shaheenbharwani/sim2real-3d-printed-quadruped/hardware/urdf/meshes/mesh163.obj

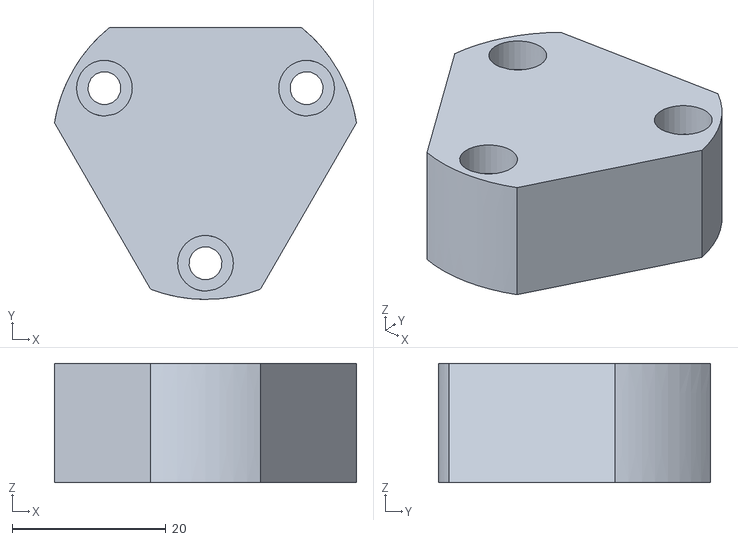
[picture p12: CAD file, 2025-07-08]
hardware/urdf/meshes/mesh163.obj
39.3 x 35.3 x 15.5
