shaheenbharwani/sim2real-3d-printed-quadruped/hardware/urdf/meshes/mesh92.obj

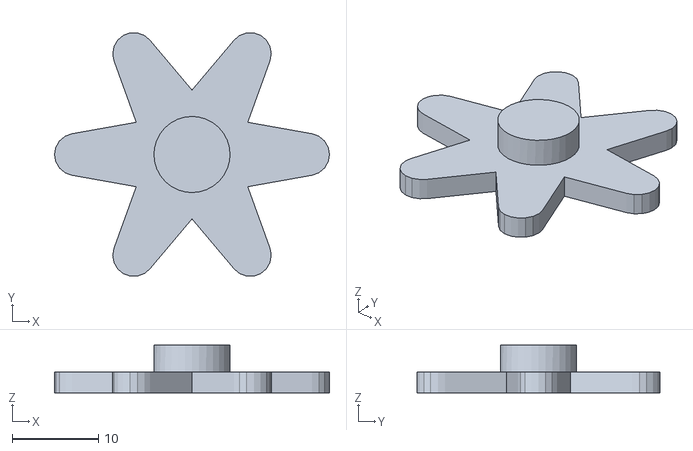
[picture p13: CAD file, 2025-07-08]
hardware/urdf/meshes/mesh92.obj
31.8 x 28.1 x 5.50
