shaheenbharwani/sim2real-3d-printed-quadruped/hardware/urdf/meshes/mesh118.obj

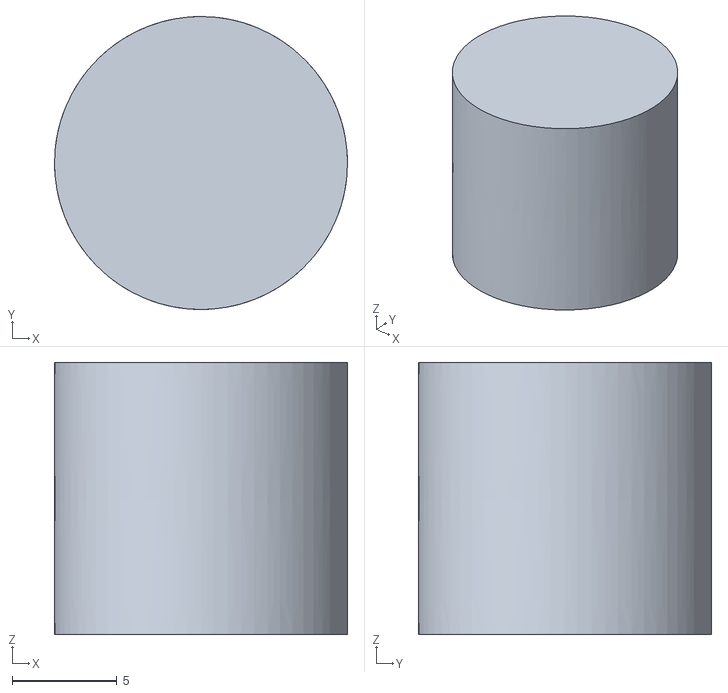
[picture p14: CAD file, 2025-07-08]
hardware/urdf/meshes/mesh118.obj
14.0 x 14.0 x 13.0
