shaheenbharwani/sim2real-3d-printed-quadruped/hardware/urdf/meshes/mesh71.obj

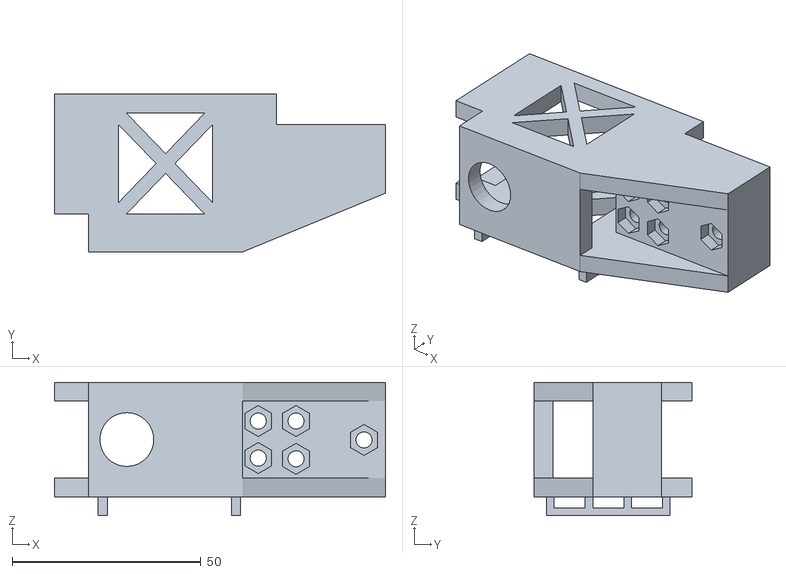
[picture p15: CAD file, 2025-07-08]
hardware/urdf/meshes/mesh71.obj
87.6 x 41.8 x 35.3
