shaheenbharwani/sim2real-3d-printed-quadruped/hardware/urdf/meshes/mesh1.obj

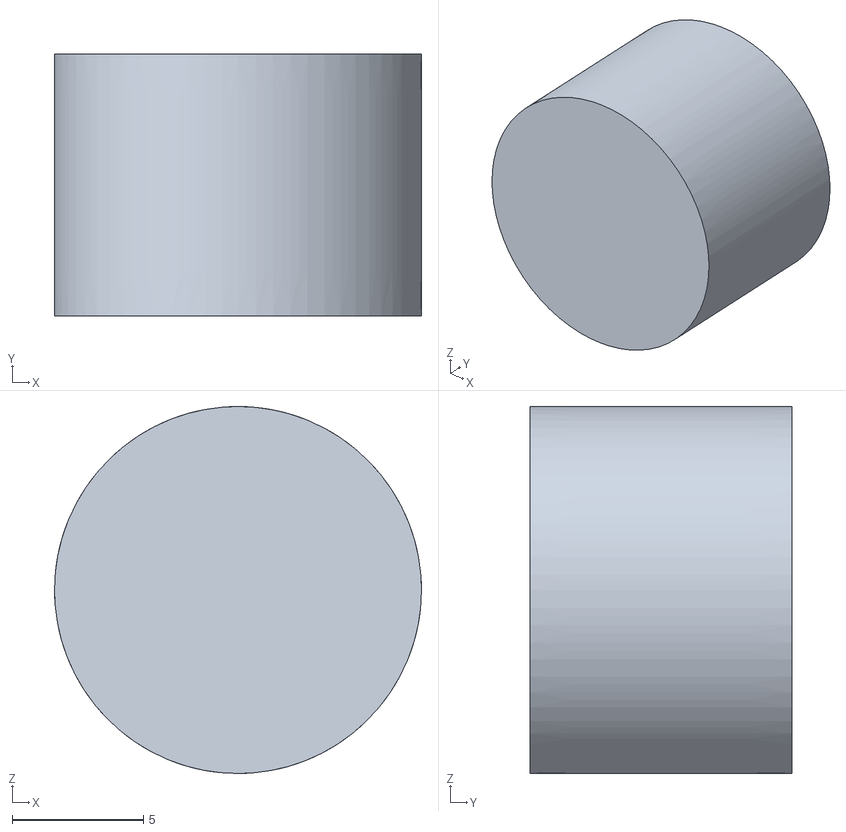
[picture p16: CAD file, 2025-07-08]
hardware/urdf/meshes/mesh1.obj
14.0 x 10.0 x 14.0
