shaheenbharwani/sim2real-3d-printed-quadruped/hardware/urdf/meshes/mesh164.obj

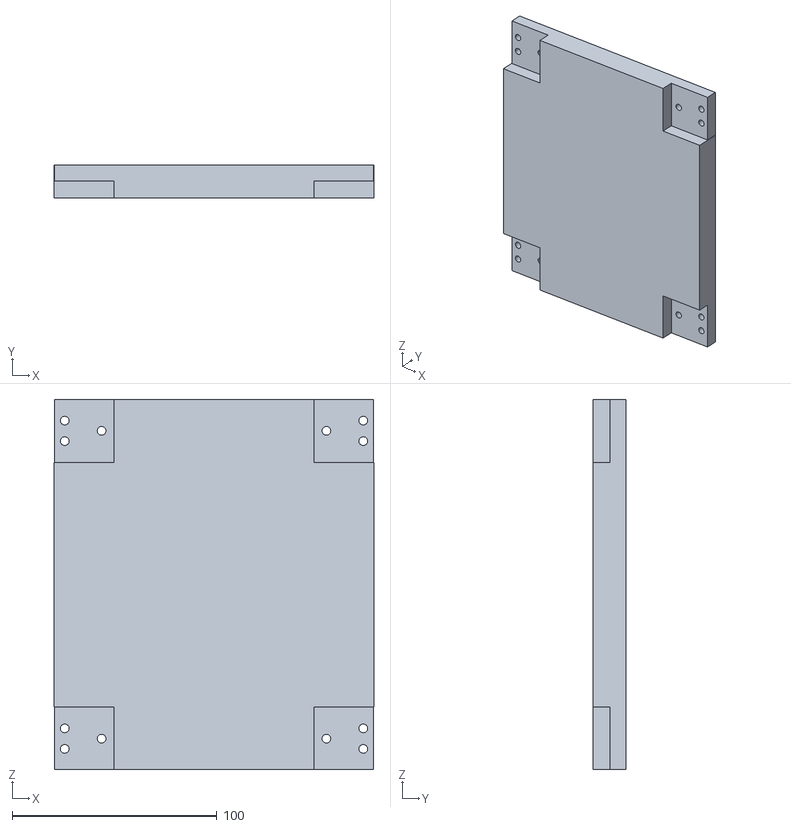
[picture p17: CAD file, 2025-07-08]
hardware/urdf/meshes/mesh164.obj
156.0 x 16.3 x 180.5
