shaheenbharwani/sim2real-3d-printed-quadruped/hardware/urdf/meshes/mesh77.obj

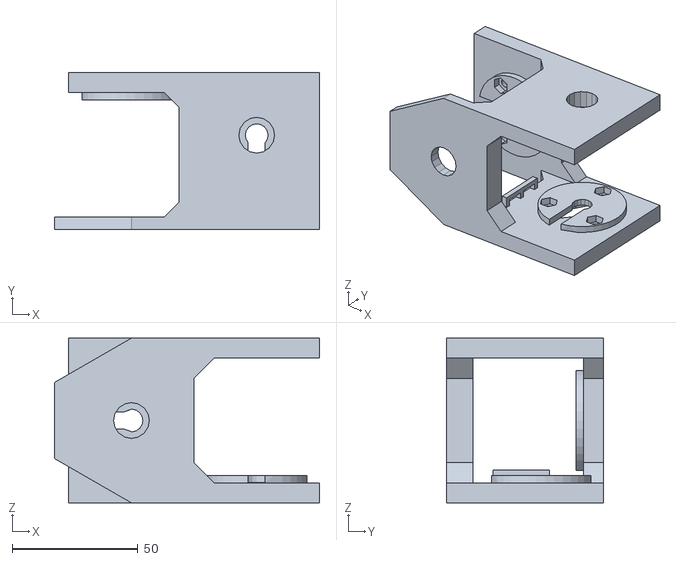
[picture p18: CAD file, 2025-07-08]
hardware/urdf/meshes/mesh77.obj
105.5 x 62.6 x 65.6
