shaheenbharwani/sim2real-3d-printed-quadruped/hardware/urdf/meshes/mesh160.obj

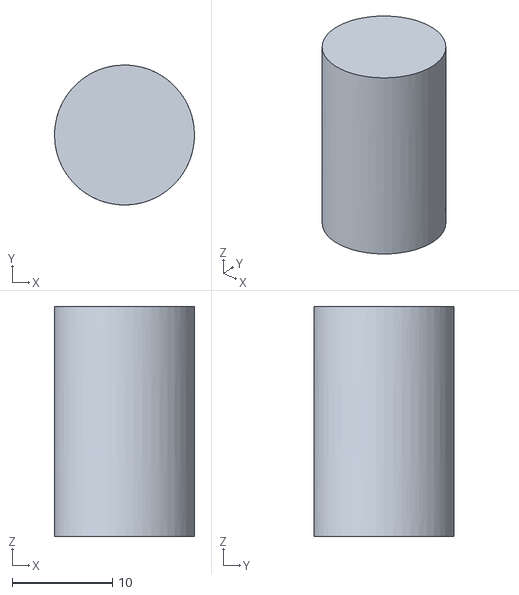
[picture p19: CAD file, 2025-07-08]
hardware/urdf/meshes/mesh160.obj
14.0 x 14.0 x 23.0
