shaheenbharwani/sim2real-3d-printed-quadruped/hardware/urdf/meshes/mesh139.obj

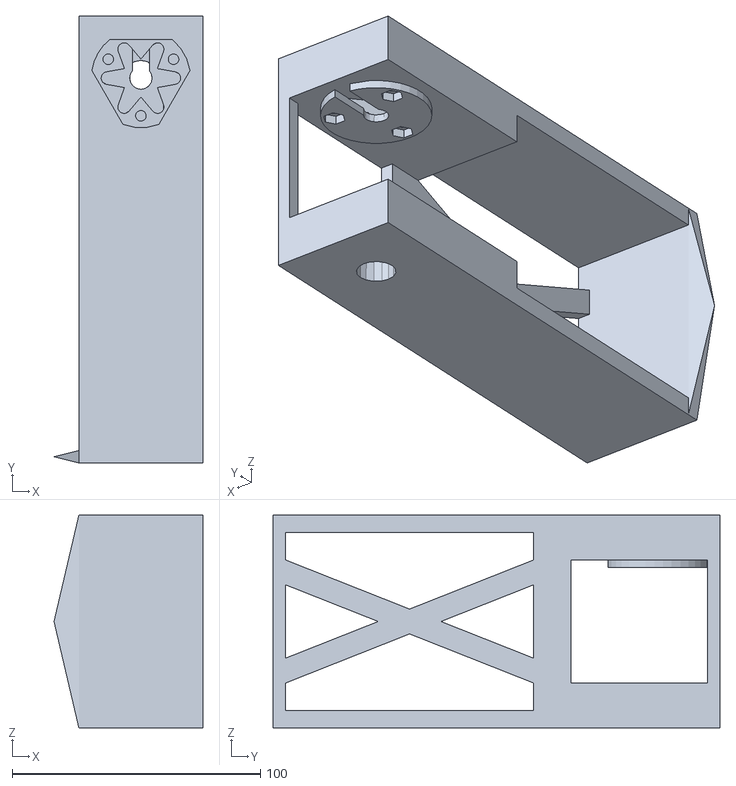
[picture p20: CAD file, 2025-07-08]
hardware/urdf/meshes/mesh139.obj
60.0 x 180.0 x 85.6
